hannes-hochreiner/sensor-node/firmware/inc/encryption.h

/*
 * encryption.h
 *
 *  Created on: Apr 18, 2017
 *      Author: Hannes Hochreiner <hannes@hochreiner.net>
 */

#ifndef INC_ENCRYPTION_H_
#define INC_ENCRYPTION_H_

#include "em_aes.h"

void encrypt();

#endif /* INC_ENCRYPTION_H_ */
