hannes-hochreiner/sensor-node/firmware/src/encryption.c

/*
 * encryption.c
 *
 *  Created on: Apr 18, 2017
 *      Author: Hannes Hochreiner <hannes@hochreiner.net>
 */

#include "encryption.h"

void encrypt() {
  // Encrypt some data
  const uint8_t plaintext[32] = {0x6B, 0xC1, 0xBE, 0xE2, 0x2E, 0x40, 0x9F, 0x96,
                              0xE9, 0x3D, 0x7E, 0x11, 0x73, 0x93, 0x17, 0x2A,
                              0xAE, 0x2D, 0x8A, 0x57, 0x1E, 0x03, 0xAC, 0x9C,
                              0x9E, 0xB7, 0x6F, 0xAC, 0x45, 0xAF, 0x8E, 0x51};
  const uint8_t key[16] = {0x2B, 0x7E, 0x15, 0x16, 0x28, 0xAE, 0xD2, 0xA6,
                        0xAB, 0xF7, 0x15, 0x88, 0x09, 0xCF, 0x4F, 0x3C};
  const uint8_t iv[16] = {0x00, 0x01, 0x02, 0x03, 0x04, 0x05, 0x06, 0x07,
                       0x08, 0x09, 0x0A, 0x0B, 0x0C, 0x0D, 0x0E, 0x0F};
  uint8_t ciphertext[32]; /* Output buffer for encrypted data (ciphertext). */
  AES_CBC128(ciphertext, plaintext, 64, key, iv, true);
}
